bororda/BT-Navigator-Controller/Docs/Boards/ESP32-36-Pin-Pinout.jpg

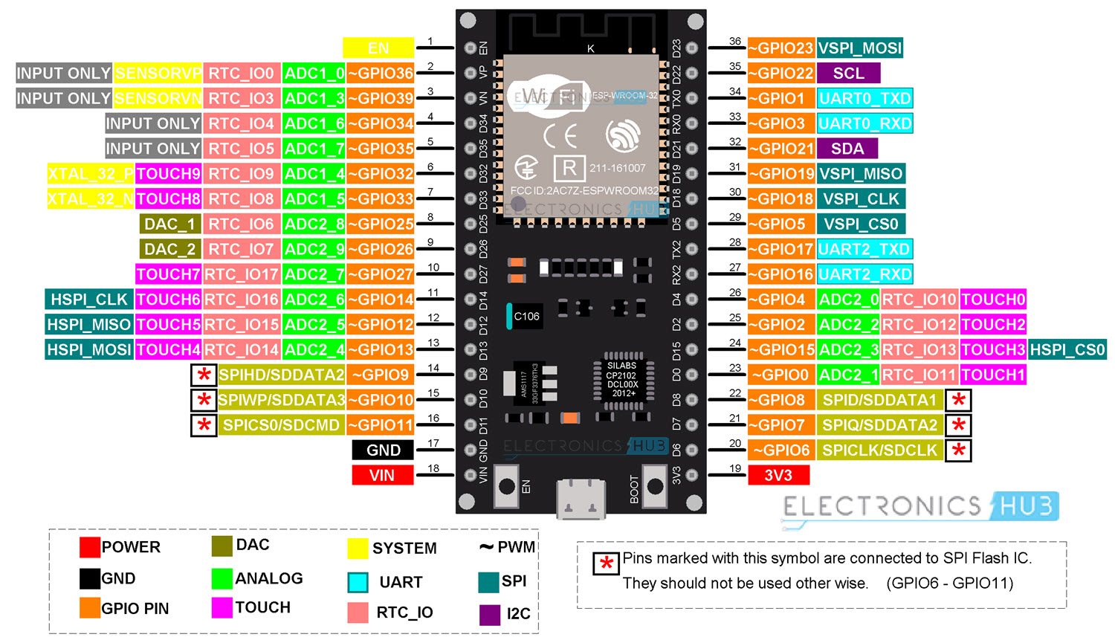
Docs/Boards/ESP32-36-Pin-Pinout.jpg
