bororda/BT-Navigator-Controller/Docs/Boards/ESP32-Pinout-1.jpg

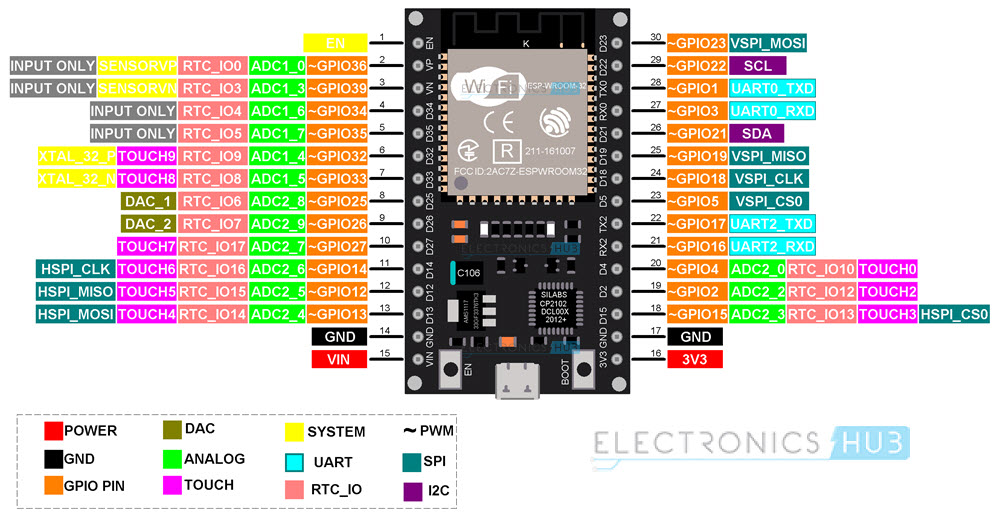
Docs/Boards/ESP32-Pinout-1.jpg
