bororda/BT-Navigator-Controller/Docs/Boards/ESP-WROOM-32-Pinout.jpg

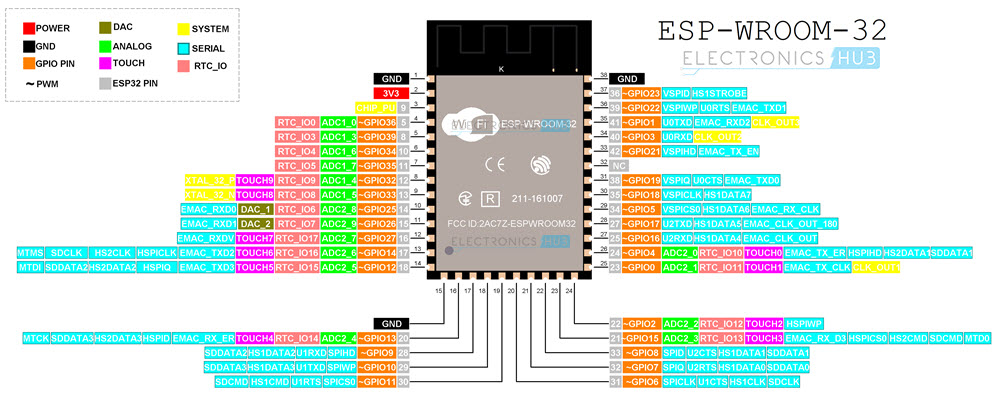
Docs/Boards/ESP-WROOM-32-Pinout.jpg
