bororda/BT-Navigator-Controller/Docs/Boards/Seeeduino-XIAO-interrupts.jpeg.webp

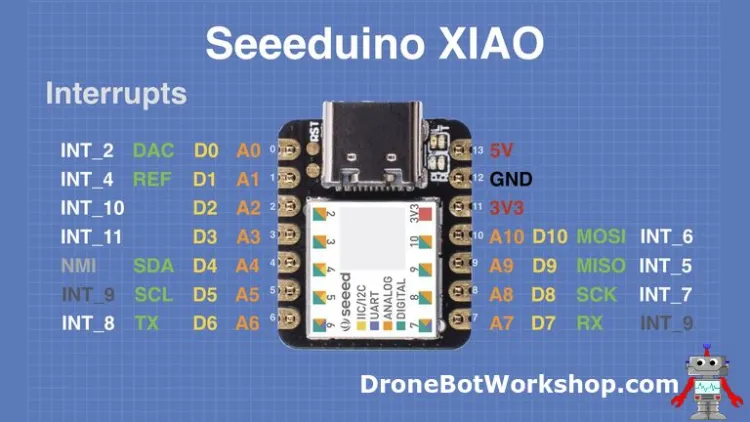
Docs/Boards/Seeeduino-XIAO-interrupts.jpeg.webp
