bororda/BT-Navigator-Controller/Docs/Pics/slim/2.png

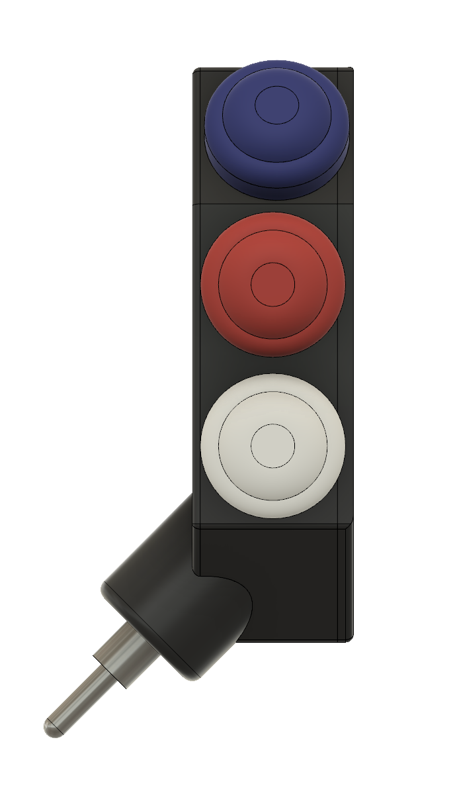
Docs/Pics/slim/2.png
