bororda/BT-Navigator-Controller/Docs/Pics/slim/3.png

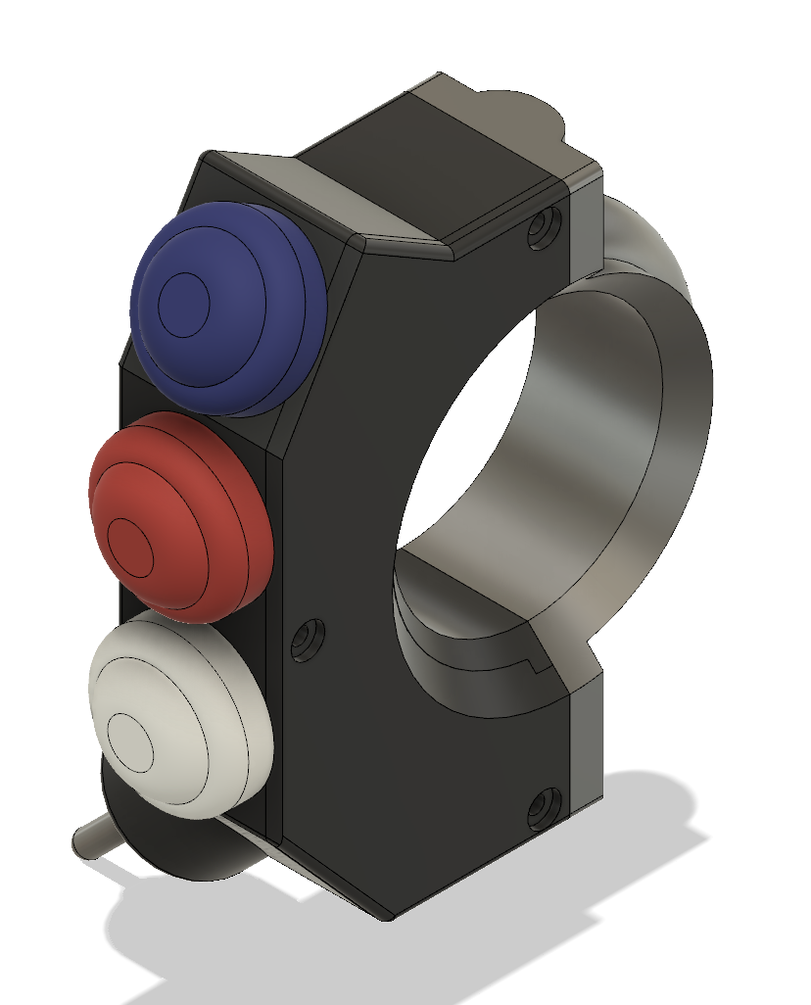
Docs/Pics/slim/3.png
