bororda/BT-Navigator-Controller/Docs/Pics/slim/IMG_2291.jpeg

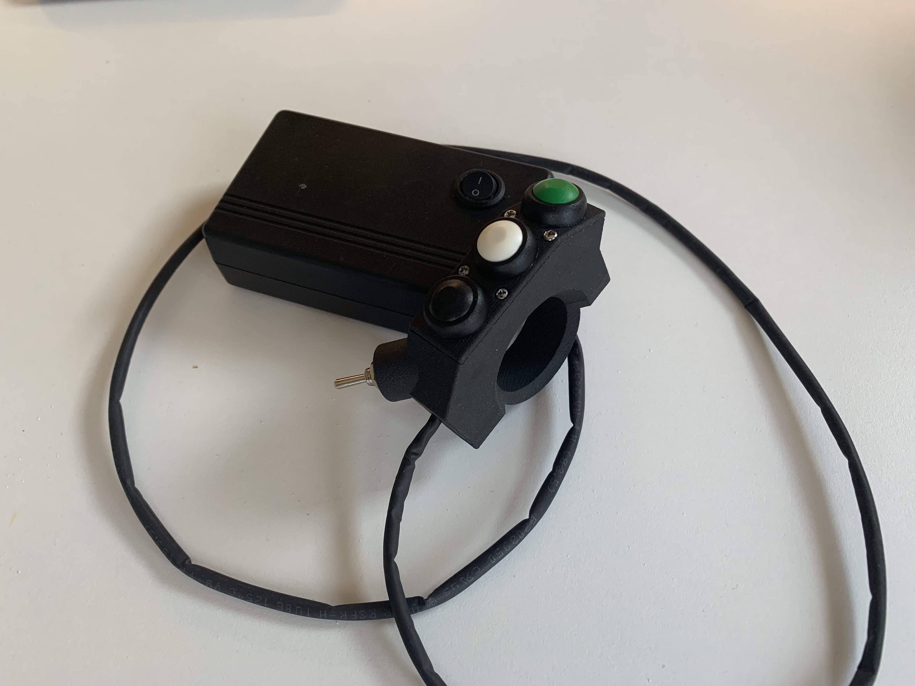
Docs/Pics/slim/IMG_2291.jpeg
