bororda/BT-Navigator-Controller/Docs/Pics/V1/1.png

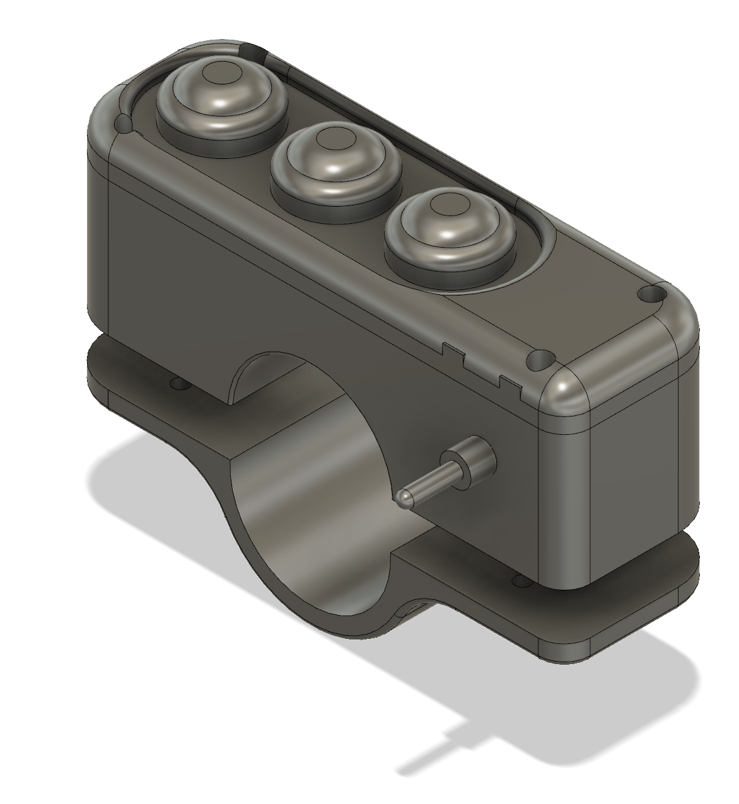
Docs/Pics/V1/1.png
