bororda/BT-Navigator-Controller/Docs/Pics/V1/2.png

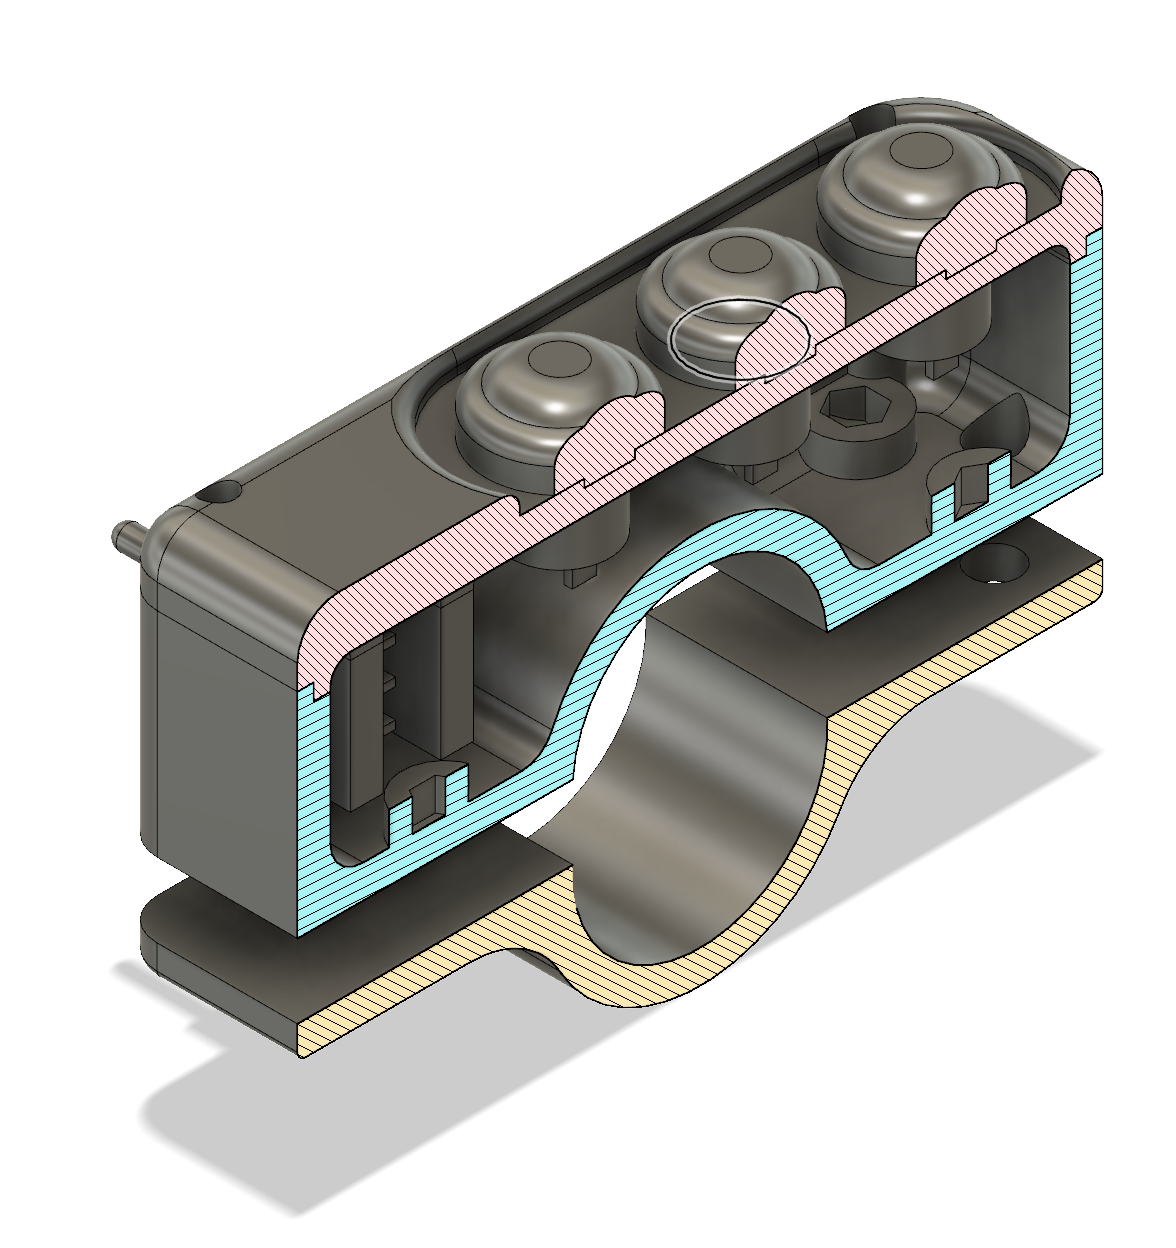
Docs/Pics/V1/2.png
