bororda/BT-Navigator-Controller/Docs/Pics/V1/IMG_2272.jpeg

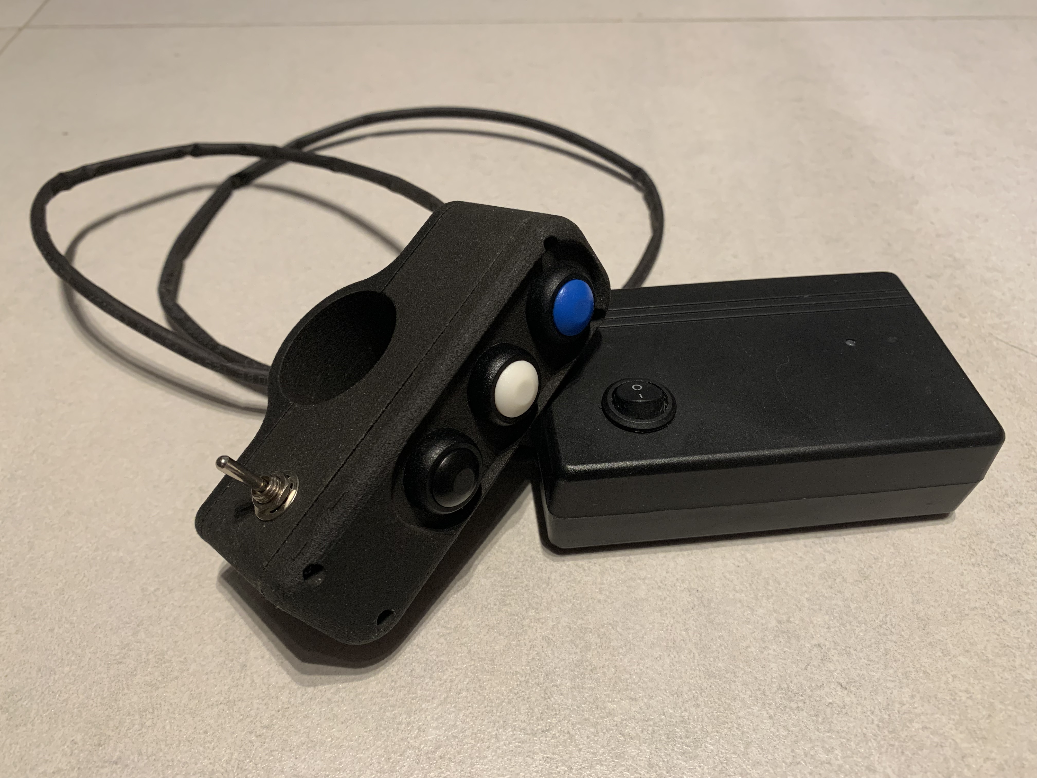
Docs/Pics/V1/IMG_2272.jpeg
