bororda/BT-Navigator-Controller/Reference project/Rampage Navigator Open Source Files v1.7.3/Circuit Design/Rampage Nav Circuit Design with permanant power & battery backup.jpg

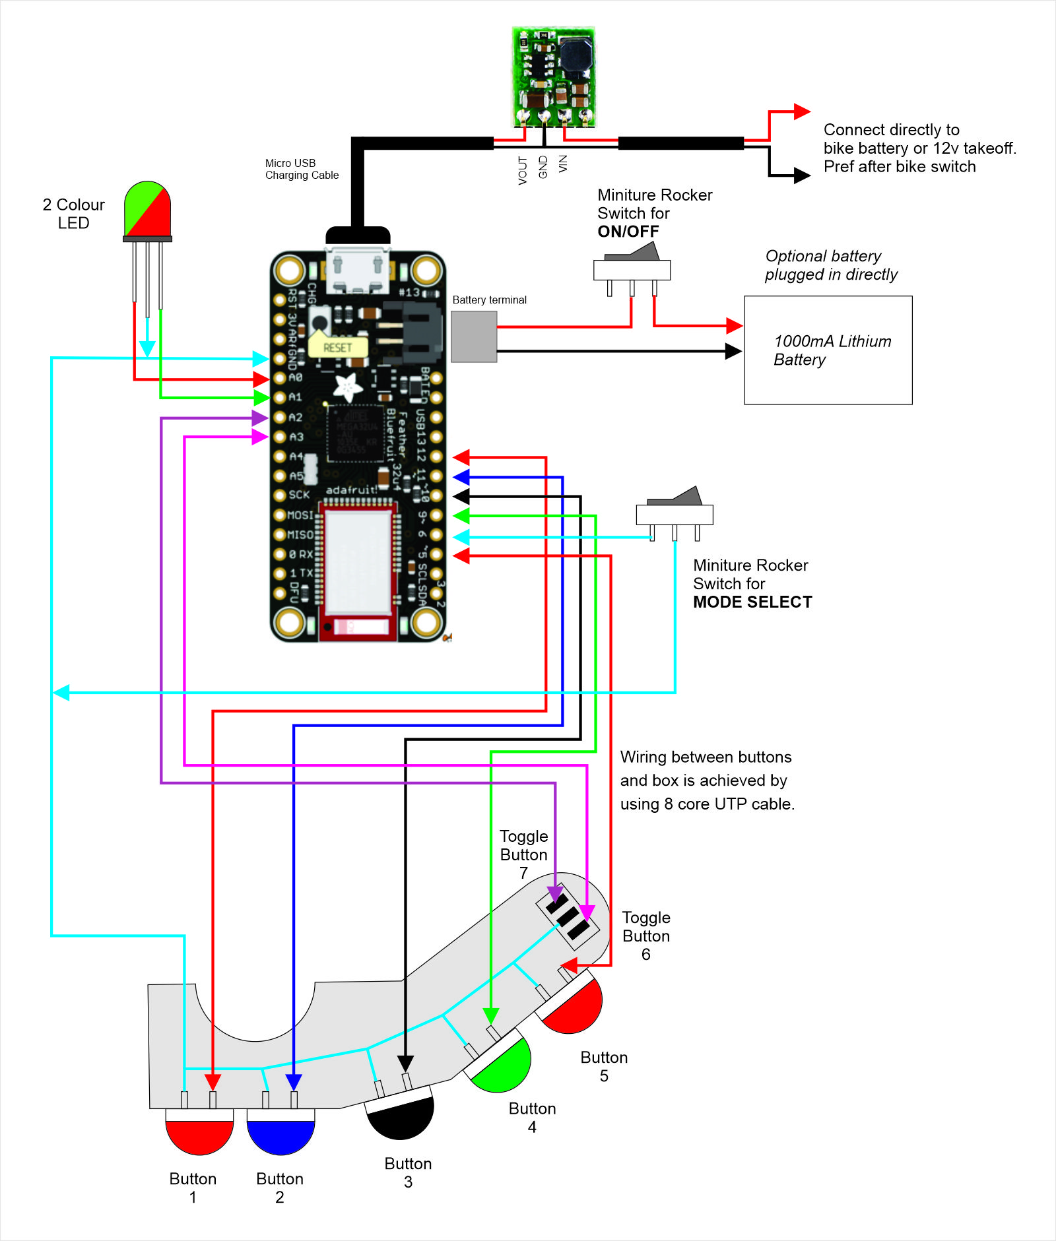
Reference project/Rampage Navigator Open Source Files v1.7.3/Circuit Design/Rampage Nav Circuit Design with permanant power & battery backup.jpg
