bororda/BT-Navigator-Controller/Reference project/Rampage Navigator Open Source Files v1.7.3/Illustration Images/WhatsApp Image 2021-06-27 at 16.28.02 (3).jpeg

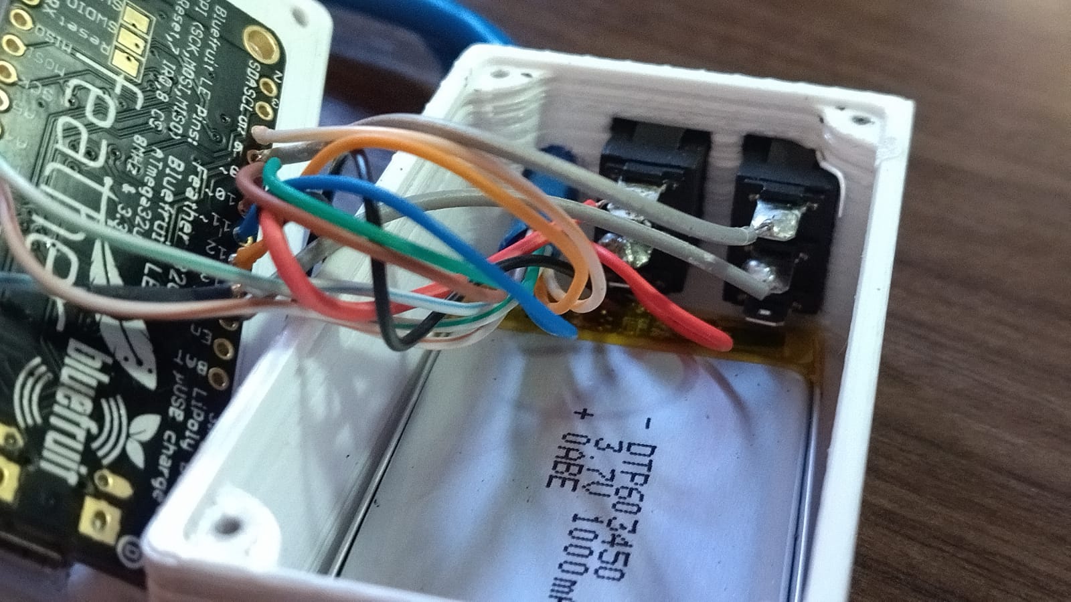
Reference project/Rampage Navigator Open Source Files v1.7.3/Illustration Images/WhatsApp Image 2021-06-27 at 16.28.02 (3).jpeg
