bororda/BT-Navigator-Controller/Reference project/Rampage Navigator Open Source Files v1.7.3/3D Print files/Bluetooth Controller v1.3 ORIGINAL SOLID DESIGN/STL Files/Bluetooth box 1.1 - Box.stl

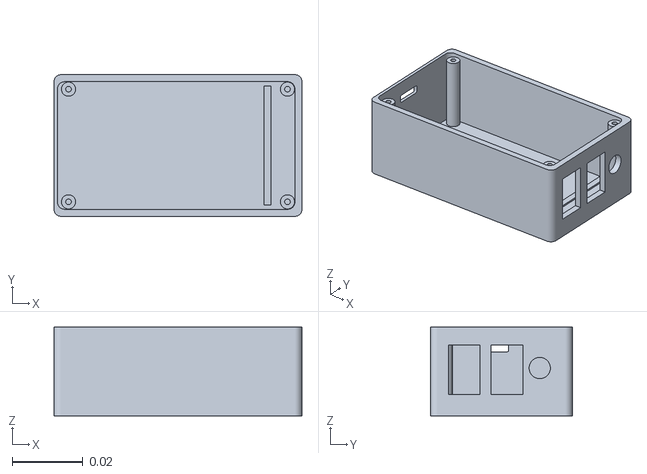
[picture p48: CAD file, 2023-03-28]
Reference project/Rampage Navigator Open Source Files v1.7.3/3D Print files/Bluetooth Controller v1.3 ORIGINAL SOLID DESIGN/STL Files/Bluetooth box 1.1 - Box.stl
0.07 x 0.04 x 0.025
