bororda/BT-Navigator-Controller/Reference project/Rampage Navigator Open Source Files v1.7.3/3D Print files/Bluetooth Controller v1.5 TWO SIDED OPTION FOR EASIER SOLDERING/STL Files/Controller button 1.5 - Back.stl

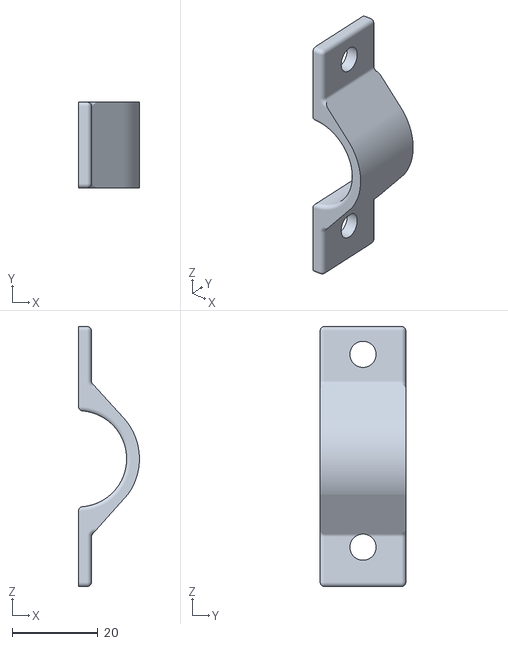
[picture p49: CAD file, 2023-03-28]
Reference project/Rampage Navigator Open Source Files v1.7.3/3D Print files/Bluetooth Controller v1.5 TWO SIDED OPTION FOR EASIER SOLDERING/STL Files/Controller button 1.5 - Back.stl
14.2 x 20.0 x 60.7
