bororda/BT-Navigator-Controller/V1/Hardware/Wiring/wiring.png

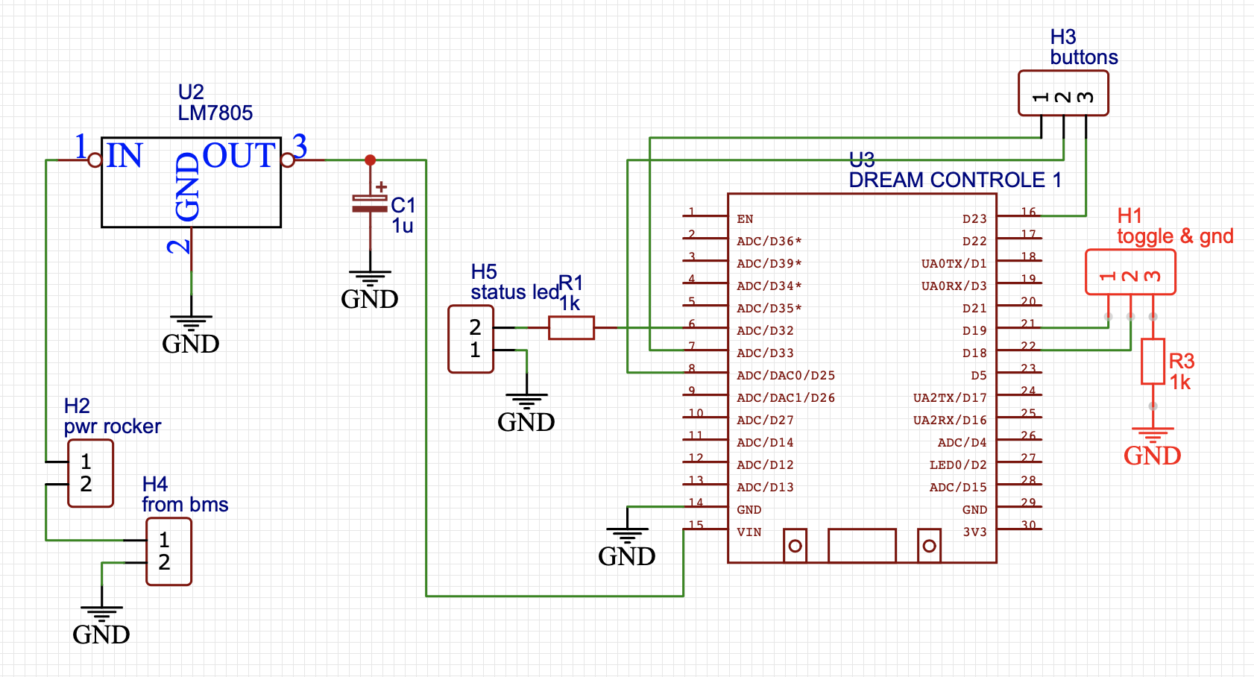
V1/Hardware/Wiring/wiring.png
